lengzhi092/BalanceCar/程序/Inc/control.h

#ifndef __CONTROL_H
#define __CONTROL_H

#include "sys.h"
/********定义端口********/
#define INT PAin(12)    //PA12连接到MPU6050的中断引脚

/********定义常量********/
#define PWMB   TIM1->CCR4  //PA11
#define BIN2   PBout(12)
#define BIN1   PBout(13)
#define AIN2   PBout(15)
#define AIN1   PBout(14)
#define PWMA   TIM1->CCR1  //PA8

#define Middle_angle 0
#define Control_Frequency  200.0    //编码器读取频率
#define PI 3.14159265
#define Diameter_67  67.0   //轮子直径67mm 
#define EncoderMultiples   4.0  //编码器倍频数
#define Encoder_precision  13.0 //编码器精度 13线
#define Reduction_Ratio  30.0   //减速比30

/********声明函数********/
u32 myabs(int a);
int Balance(float angle,float gyro);
int Velocity(int encoder_left,int encoder_right);
int Turn(float gyro);

void Set_Pwm(int motor_left,int motor_right);

int PWM_Limit(int IN,int max,int min);
u8 Turn_Off(float angle, int voltage);

#endif
