lengzhi092/BalanceCar/程序/Inc/sys.h

#ifndef __SYS_H
#define __SYS_H	
#include "stm32f1xx.h"

//定义一些常用的数据类型短关键字 
typedef int32_t  s32;
typedef int16_t s16;
typedef int8_t  s8;

typedef const int32_t sc32;  
typedef const int16_t sc16;  
typedef const int8_t sc8;  

typedef __IO int32_t  vs32;
typedef __IO int16_t  vs16;
typedef __IO int8_t   vs8;

typedef __I int32_t vsc32;  
typedef __I int16_t vsc16; 
typedef __I int8_t vsc8;   

typedef uint32_t  u32;
typedef uint16_t u16;
typedef uint8_t  u8;

typedef const uint32_t uc32;  
typedef const uint16_t uc16;  
typedef const uint8_t uc8; 

typedef __IO uint32_t  vu32;
typedef __IO uint16_t vu16;
typedef __IO uint8_t  vu8;

typedef __I uint32_t vuc32;  
typedef __I uint16_t vuc16; 
typedef __I uint8_t vuc8;  		

/*  位带操作,实现51类似的GPIO控制功能
    具体实现思想,参考<<CM3权威指南>>第五章(87页~92页).
    IO口操作宏定义    */
#define BITBAND(addr, bitnum) ((addr & 0xF0000000)+0x2000000+((addr &0xFFFFF)<<5)+(bitnum<<2)) 
#define MEM_ADDR(addr)  *((volatile unsigned long  *)(addr)) 
#define BIT_ADDR(addr, bitnum)   MEM_ADDR(BITBAND(addr, bitnum)) 
            /*******IO口地址映射*******/
#define GPIOA_ODR_Addr    (GPIOA_BASE+12) //0x4001080C 
#define GPIOB_ODR_Addr    (GPIOB_BASE+12) //0x40010C0C 
#define GPIOC_ODR_Addr    (GPIOC_BASE+12) //0x4001100C 
#define GPIOD_ODR_Addr    (GPIOD_BASE+12) //0x4001140C 
#define GPIOE_ODR_Addr    (GPIOE_BASE+12) //0x4001180C 
#define GPIOF_ODR_Addr    (GPIOF_BASE+12) //0x40011A0C    
#define GPIOG_ODR_Addr    (GPIOG_BASE+12) //0x40011E0C    

#define GPIOA_IDR_Addr    (GPIOA_BASE+8) //0x40010808 
#define GPIOB_IDR_Addr    (GPIOB_BASE+8) //0x40010C08 
#define GPIOC_IDR_Addr    (GPIOC_BASE+8) //0x40011008 
#define GPIOD_IDR_Addr    (GPIOD_BASE+8) //0x40011408 
#define GPIOE_IDR_Addr    (GPIOE_BASE+8) //0x40011808 
#define GPIOF_IDR_Addr    (GPIOF_BASE+8) //0x40011A08 
#define GPIOG_IDR_Addr    (GPIOG_BASE+8) //0x40011E08 
 
//IO口操作,只对单一的IO口!
//确保n的值小于16!
#define PAout(n)   BIT_ADDR(GPIOA_ODR_Addr,n)  //输出 
#define PAin(n)    BIT_ADDR(GPIOA_IDR_Addr,n)  //输入 

#define PBout(n)   BIT_ADDR(GPIOB_ODR_Addr,n)  //输出 
#define PBin(n)    BIT_ADDR(GPIOB_IDR_Addr,n)  //输入 

#define PCout(n)   BIT_ADDR(GPIOC_ODR_Addr,n)  //输出 
#define PCin(n)    BIT_ADDR(GPIOC_IDR_Addr,n)  //输入 

#define PDout(n)   BIT_ADDR(GPIOD_ODR_Addr,n)  //输出 
#define PDin(n)    BIT_ADDR(GPIOD_IDR_Addr,n)  //输入 

#define PEout(n)   BIT_ADDR(GPIOE_ODR_Addr,n)  //输出 
#define PEin(n)    BIT_ADDR(GPIOE_IDR_Addr,n)  //输入

#define PFout(n)   BIT_ADDR(GPIOF_ODR_Addr,n)  //输出 
#define PFin(n)    BIT_ADDR(GPIOF_IDR_Addr,n)  //输入

#define PGout(n)   BIT_ADDR(GPIOG_ODR_Addr,n)  //输出 
#define PGin(n)    BIT_ADDR(GPIOG_IDR_Addr,n)  //输入

extern float Angle_Balance,Gyro_Balance,Gyro_Turn; //平衡倾角 平衡陀螺仪 转向陀螺仪
extern float Velocity_Left,Velocity_Right;
extern int Temperature;
extern float Acceleration_Z; 
extern int Voltage;
extern volatile u8 delay_flag,delay_50; //提供延时的变量
extern u8 Flag_Stop,Flag_Show;
extern int Motor_Left,Motor_Right;
extern u8 Flag_front,Flag_back,Flag_Left,Flag_Right,Flag_velocity;
extern float Balance_Kp,Balance_Kd,Velocity_Kp,Velocity_Ki,Turn_Kp,Turn_Kd;
extern u8 PID_Send;

#include <math.h>
#include <string.h> 
#include <stdio.h>
#include <stdint.h>
#include <stdlib.h>
#include "main.h"
#include "delay.h"
#include "ioi2c.h"
#include "control.h"
#include "filter.h"
#include "mpu6050.h"
#include "oled.h"
#include "adc.h"
#include "tim.h"
#include "usart.h"
#include "gpio.h"
    #include "inv_mpu.h"    //要用DMP触发的数据就绪中断，这四个文件就像链式反应，改一点就很容易一堆错误
    #include "inv_mpu_dmp_motion_driver.h"
    #include "dmpKey.h"
    #include "dmpmap.h"
#include "encoder.h"
#include "key.h"
#include "DataSend.h"

#endif
