lengzhi092/BalanceCar/程序/Src/adc.c

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
/* Includes ------------------------------------------------------------------*/
#include "adc.h"

ADC_HandleTypeDef hadc1;

/* ADC1 init function */
void MX_ADC1_Init(void)
{

  ADC_ChannelConfTypeDef sConfig = {0};

  /** Common config
  */
  hadc1.Instance = ADC1;
  hadc1.Init.ScanConvMode = ADC_SCAN_DISABLE;
  hadc1.Init.ContinuousConvMode = DISABLE;
  hadc1.Init.DiscontinuousConvMode = DISABLE;
  hadc1.Init.ExternalTrigConv = ADC_SOFTWARE_START;
  hadc1.Init.DataAlign = ADC_DATAALIGN_RIGHT;
  hadc1.Init.NbrOfConversion = 1;
  if (HAL_ADC_Init(&hadc1) != HAL_OK)
  {
    Error_Handler();
  }
  /** Configure Regular Channel
  */
  sConfig.Channel = ADC_CHANNEL_6;
  sConfig.Rank = ADC_REGULAR_RANK_1;
  sConfig.SamplingTime = ADC_SAMPLETIME_1CYCLE_5;
  if (HAL_ADC_ConfigChannel(&hadc1, &sConfig) != HAL_OK)
  {
    Error_Handler();
  }
  /* USER CODE BEGIN ADC1_Init 2 */
   HAL_ADCEx_Calibration_Start(&hadc1); //校准ADC，不校准会导致ADC测量不准确
  /* USER CODE END ADC1_Init 2 */

}

void HAL_ADC_MspInit(ADC_HandleTypeDef* adcHandle)
{

  GPIO_InitTypeDef GPIO_InitStruct = {0};
  if(adcHandle->Instance==ADC1)
  {
    /* ADC1 clock enable */
    __HAL_RCC_ADC1_CLK_ENABLE();

    __HAL_RCC_GPIOA_CLK_ENABLE();
    /**ADC1 GPIO Configuration
    PA6     ------> ADC1_IN6
    */
    GPIO_InitStruct.Pin = ADC_Pin;
    GPIO_InitStruct.Mode = GPIO_MODE_ANALOG;
    HAL_GPIO_Init(ADC_GPIO_Port, &GPIO_InitStruct);

  }
}

void HAL_ADC_MspDeInit(ADC_HandleTypeDef* adcHandle)
{

  if(adcHandle->Instance==ADC1)
  {
    /* Peripheral clock disable */
    __HAL_RCC_ADC1_CLK_DISABLE();

    /**ADC1 GPIO Configuration
    PA6     ------> ADC1_IN6
    */
    HAL_GPIO_DeInit(ADC_GPIO_Port, ADC_Pin);

  }
}

/* USER CODE BEGIN 1 */
/**
    ****************************************************************************
    *@brief      读取电池电压
    *@param      无
    *@retval     电池电压 单位MV
    ****************************************************************************
    */
int Get_battery_volt(void)  
{ 
   	int Volt;
    HAL_ADC_Start(&hadc1);  //开启ADC
    HAL_ADC_PollForConversion(&hadc1,10);   //轮询转换
    Volt = (u16)HAL_ADC_GetValue(&hadc1)*3.3*11*100/4096;   //电阻分压，具体根据原理图简单分析可以得到	
	return Volt;  //返回最近一次ADC1规则组的转换结果
}

/* USER CODE END 1 */
