lengzhi092/BalanceCar/程序/Inc/IOI2C.h

#ifndef __IOI2C_H
#define __IOI2C_H

#include "sys.h"

//IO方向设置
#define SDA_IN()  {GPIOB->CRH&=0XFFFFFF0F;GPIOB->CRH|=8<<4;}
#define SDA_OUT() {GPIOB->CRH&=0XFFFFFF0F;GPIOB->CRH|=3<<4;}

//IO操作函数	 
#define IIC_SCL    PBout(8) //SCL
#define IIC_SDA    PBout(9) //SDA	 
#define READ_SDA   PBin(9)  //输入SDA 

//IIC所有操作函数
void IIC_Init(void);           //初始化IIC的IO口				 
int IIC_Start(void);					 //发送IIC开始信号
void IIC_Stop(void);	  			 //发送IIC停止信号
void IIC_Send_Byte(u8 txd);		 //IIC发送一个字节
u8 IIC_Read_Byte(unsigned char ack);//IIC读取一个字节
int IIC_Wait_Ack(void); 			 //IIC等待ACK信号
void IIC_Ack(void);						 //IIC发送ACK信号
void IIC_NAck(void);					 //IIC不发送ACK信号

void IIC_Write_One_Byte(u8 daddr,u8 addr,u8 data);
u8 IIC_Read_One_Byte(u8 daddr,u8 addr);	 

u8 I2C_ReadOneByte(u8 I2C_Addr,u8 addr);
u8 IICwriteByte(u8 dev, u8 reg, u8 data);
u8 IICwriteBytes(u8 dev, u8 reg, u8 length, u8* data);
u8 IICwriteBits(u8 dev,u8 reg,u8 bitStart,u8 length,u8 data);
u8 IICwriteBit(u8 dev,u8 reg,u8 bitNum,u8 data);
u8 IICreadBytes(u8 dev, u8 reg, u8 length, u8 *data);

int i2cWrite(uint8_t addr, uint8_t reg, uint8_t len, uint8_t *data);
int i2cRead(uint8_t addr, uint8_t reg, uint8_t len, uint8_t *buf);

#endif
