lengzhi092/BalanceCar/程序/Inc/filter.h

#ifndef __FILTER_H
#define __FILTER_H

/********声明函数********/
float Kalman_Filter_x(float Accel,float Gyro);
float Complementary_Filter_x(float angle_m, float gyro_m);
float Kalman_Filter_y(float Accel,float Gyro);
float Complementary_Filter_y(float angle_m, float gyro_m);
#endif
