lengzhi092/BalanceCar/程序/Inc/key.h

#ifndef __KEY_H
#define __KEY_H

#include "sys.h"

/********定义端口********/
#define KEY PAin(5)

/********声明函数********/
u8 click_N_Double (u8 time);  //单击按键扫描和双击按键扫描
u8 click(void);               //单击按键扫描
u8 Long_Press(void);           //长按扫描  
void Key(void);
#endif
